Alex-SJuice/Hack-Piano/assets/case_done_wowowow.png

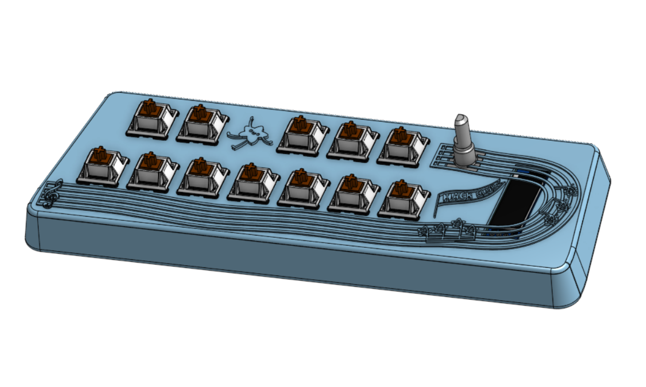
assets/case_done_wowowow.png
