Alex-SJuice/Hack-Piano/assets/wip_pics/3dview_wip.png

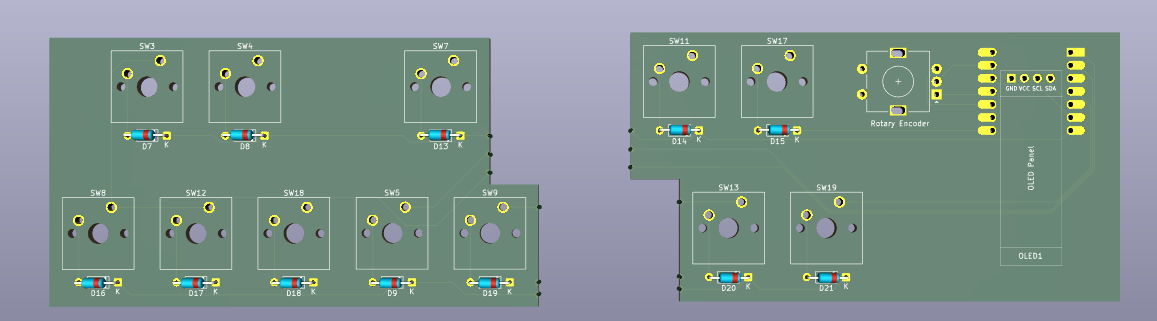
assets/wip_pics/3dview_wip.png
