Alex-SJuice/Hack-Piano/assets/wip_pics/case_details.png

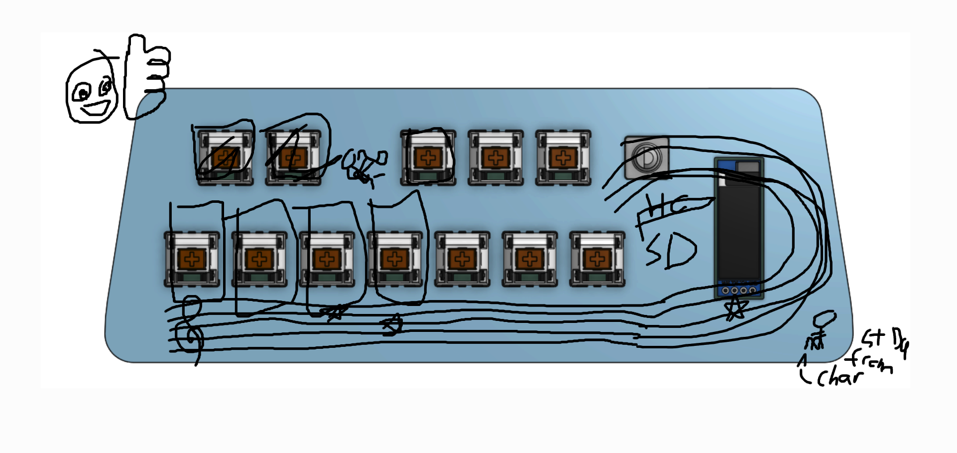
assets/wip_pics/case_details.png
