Alex-SJuice/Hack-Piano/assets/wip_pics/case_details_done.png

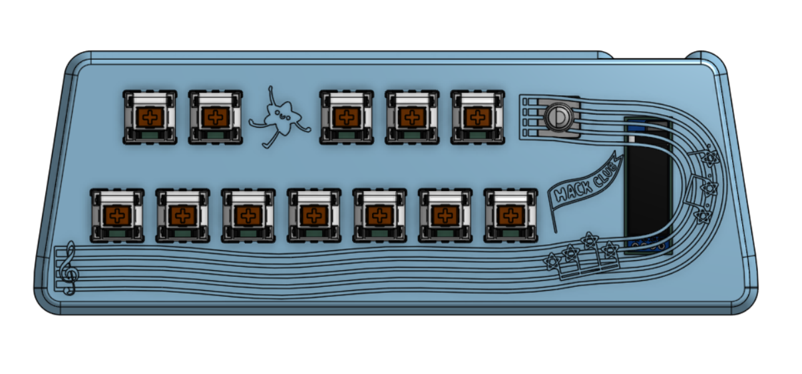
assets/wip_pics/case_details_done.png
