Alex-SJuice/Hack-Piano/assets/wip_pics/case_wip1.png

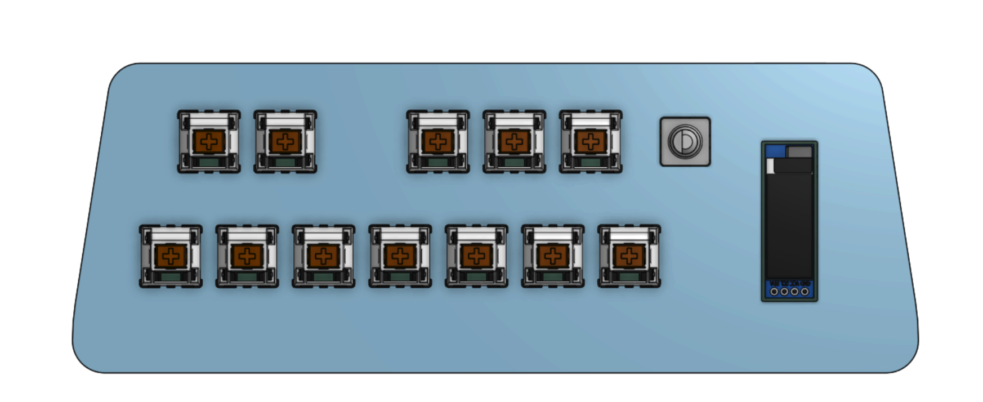
assets/wip_pics/case_wip1.png
