Alex-SJuice/Hack-Piano/assets/wip_pics/erm.png

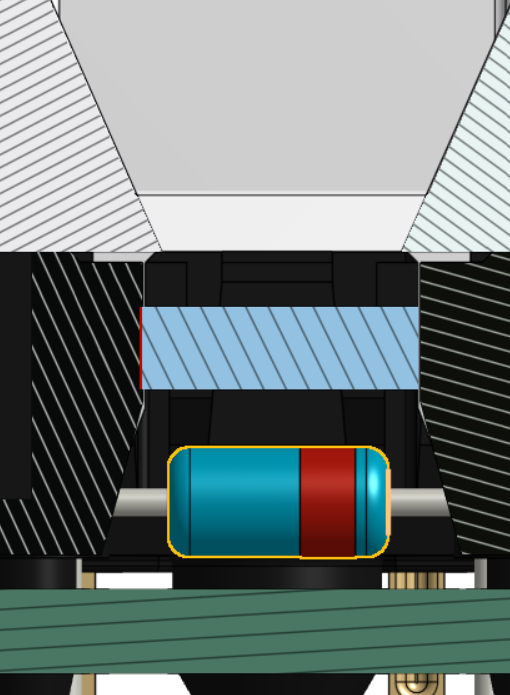
assets/wip_pics/erm.png
