Alex-SJuice/Hack-Piano/assets/wip_pics/firmware_troubles_1.png

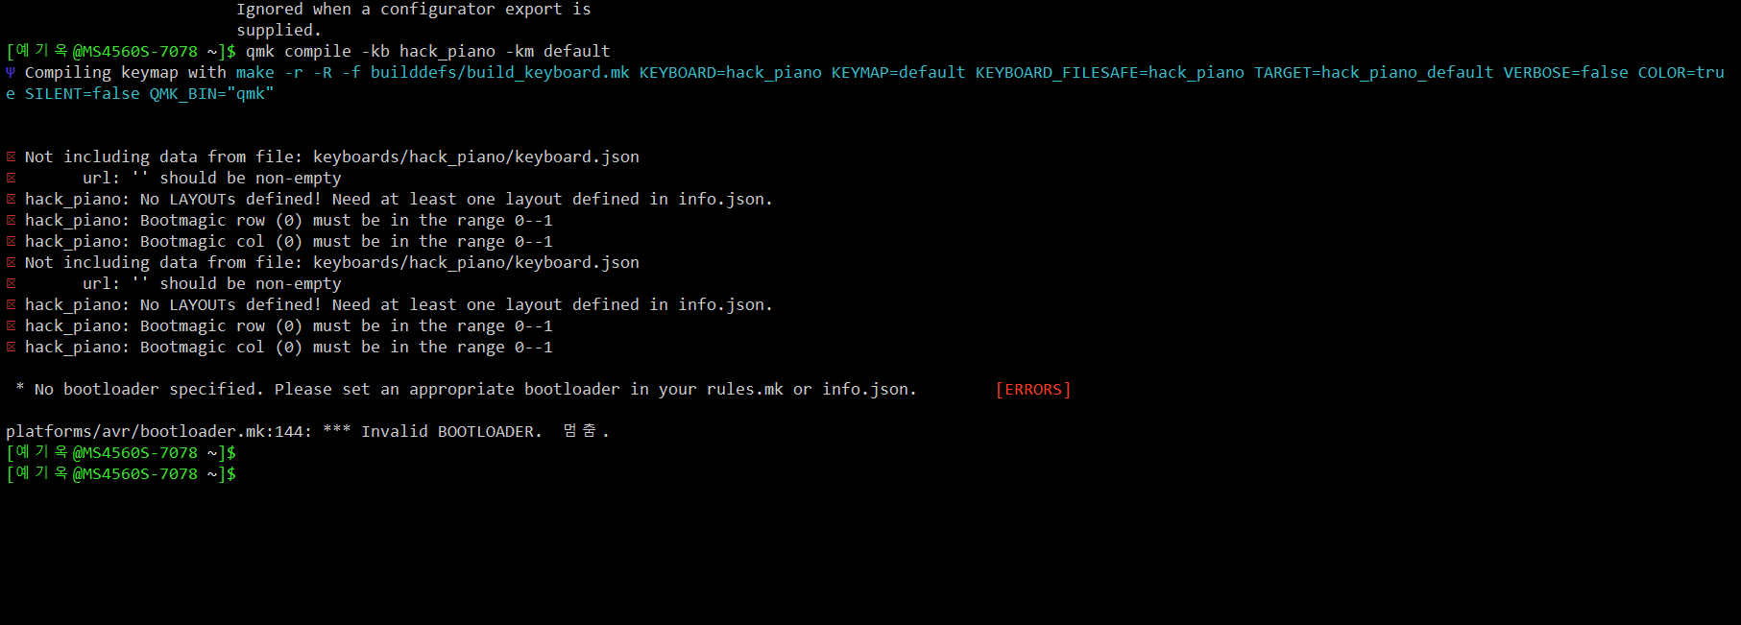
assets/wip_pics/firmware_troubles_1.png
