Alex-SJuice/Hack-Piano/assets/wip_pics/mouse_bites.png

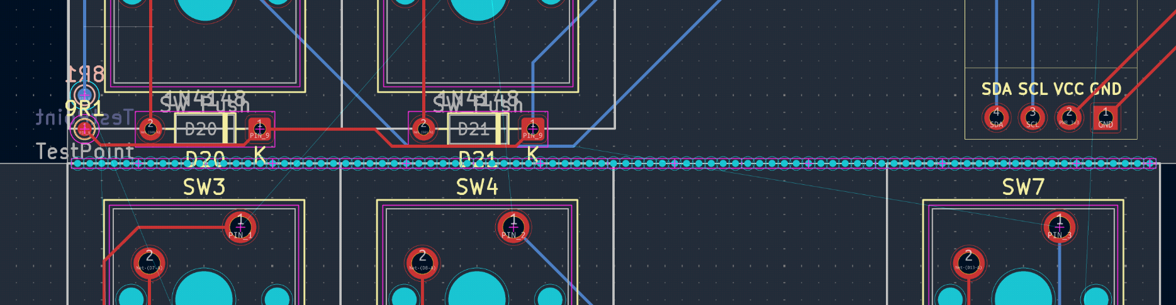
assets/wip_pics/mouse_bites.png
