Alex-SJuice/Hack-Piano/assets/wip_pics/not_curved.png

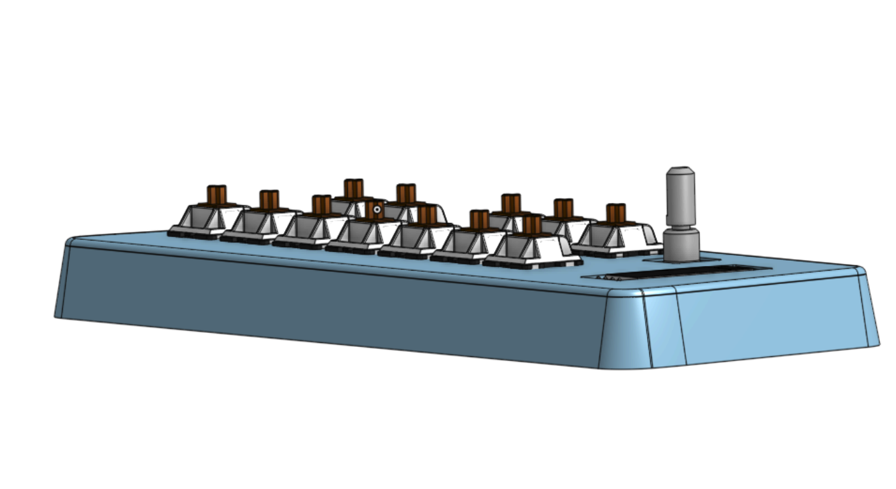
assets/wip_pics/not_curved.png
