Alex-SJuice/Hack-Piano/assets/wip_pics/pcb_done_maybe.png

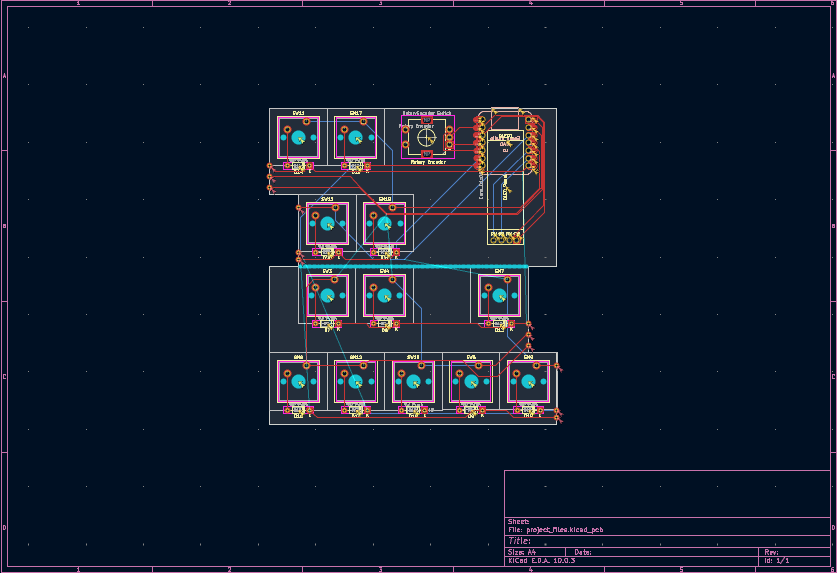
assets/wip_pics/pcb_done_maybe.png
