Alex-SJuice/Hack-Piano/assets/wip_pics/pcb_wip2.png

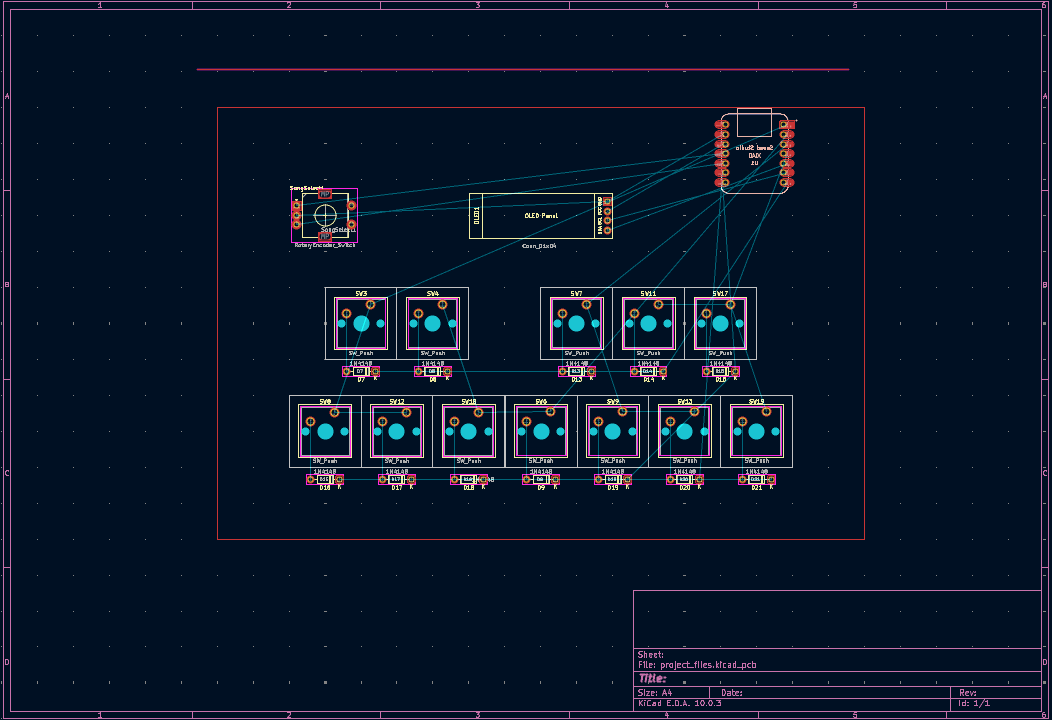
assets/wip_pics/pcb_wip2.png
