Alex-SJuice/Hack-Piano/assets/wip_pics/pcb_wip5.png

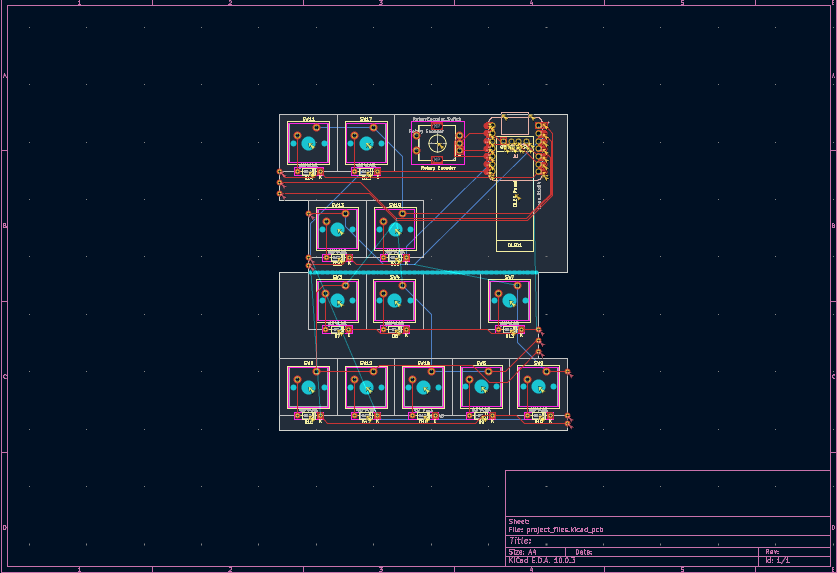
assets/wip_pics/pcb_wip5.png
