Alex-SJuice/Hack-Piano/assets/wip_pics/pcb_wip.png

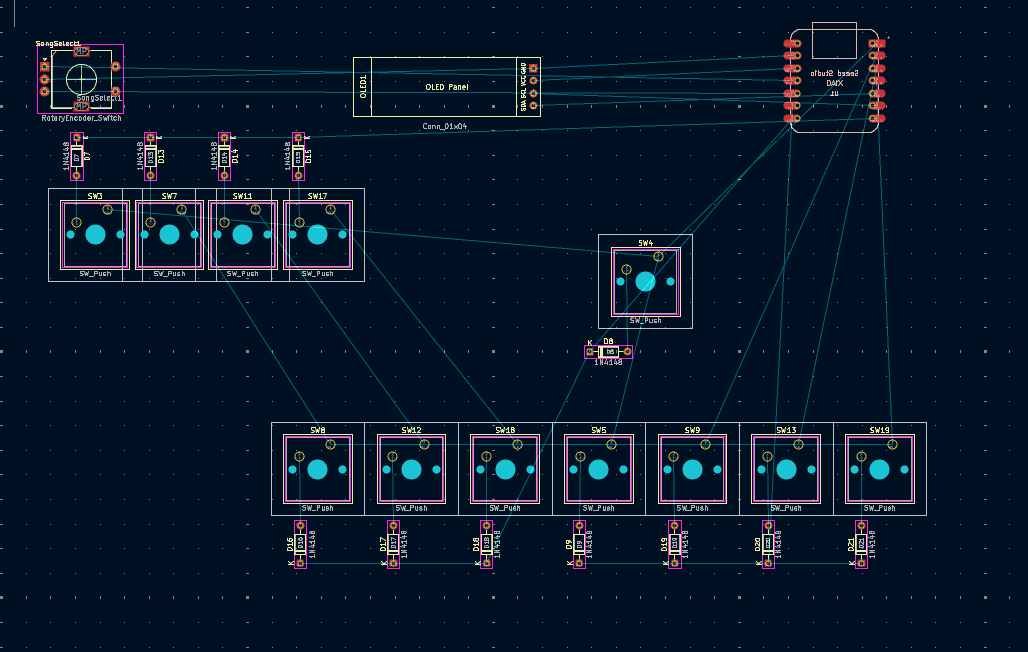
assets/wip_pics/pcb_wip.png
