Alex-SJuice/Hack-Piano/assets/wip_pics/schem_done.png

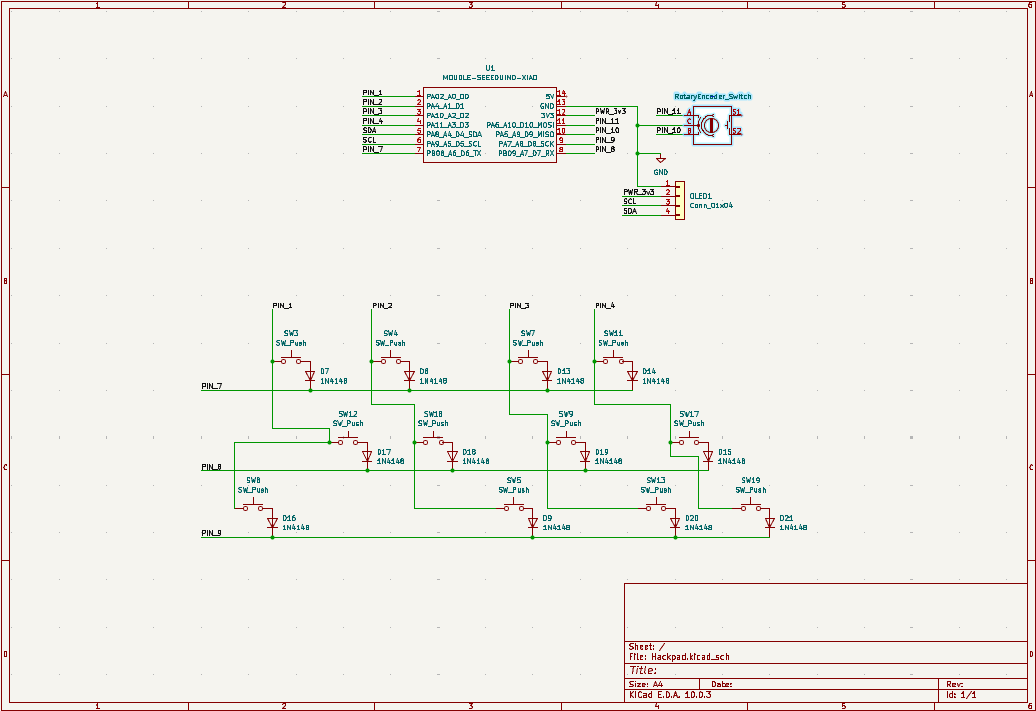
assets/wip_pics/schem_done.png
