Alex-SJuice/Hack-Piano/assets/wip_pics/uhm.png

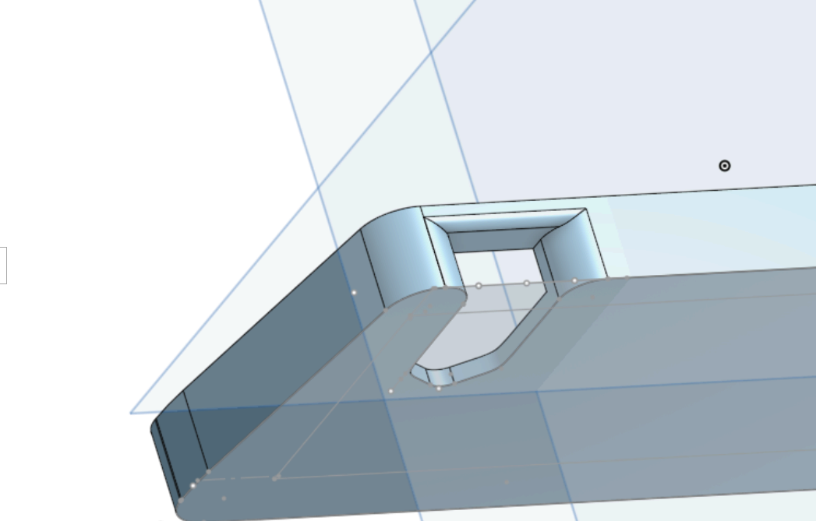
assets/wip_pics/uhm.png
